compsust/openCollector/Website_Development/images/nathaniel.jpg

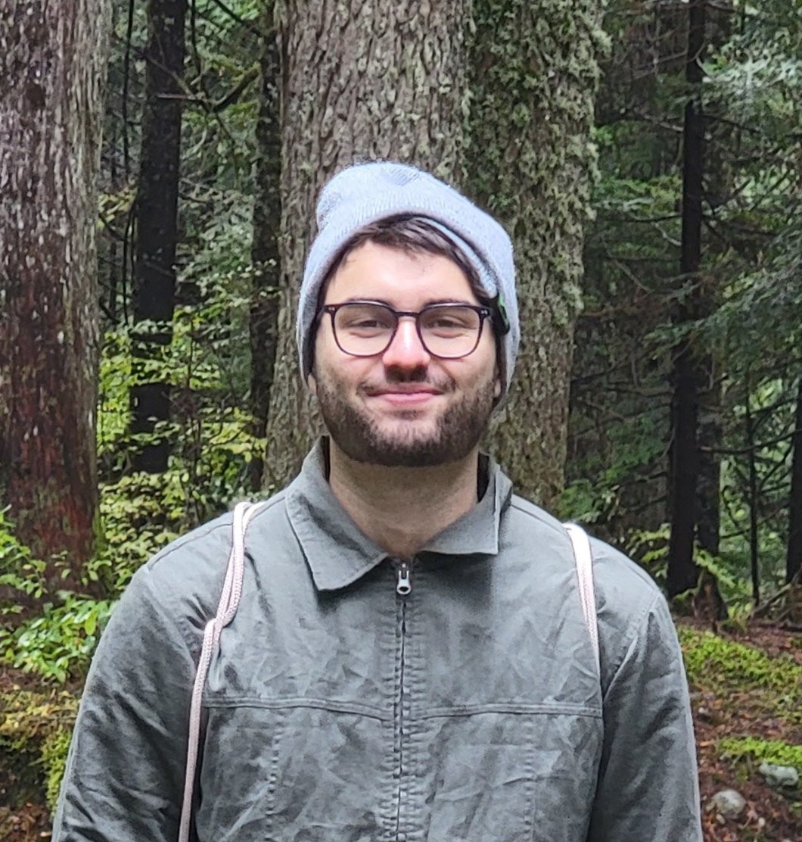
Website_Development/images/nathaniel.jpg
