compsust/openCollector/Website_Development/images/tianna.jpg

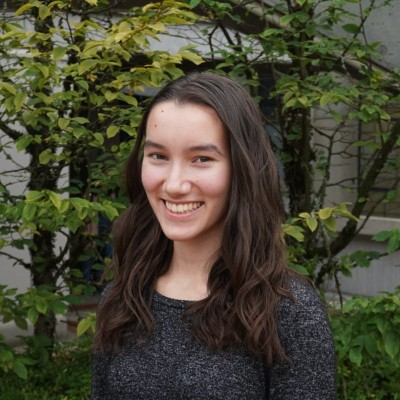
Website_Development/images/tianna.jpg
