compsust/openCollector/collector/src/sensors/drivers/DHT20/micropython.py

# MC: 02/21/2025, Complete implmentation
# MC: 03/07/2025, Added initilization

import machine
import utime

from ....config import SensorConfig
from ....datastructures import SensorData
from ...driver import AbstractSensorDriver


class DHT20SensorDriverMicropython(AbstractSensorDriver):
    """
    Implementation of the Dht20 Sensor Driver for micropython.
    """

    def __init__(self, config: SensorConfig):
        """Initialize the sensor driver with an I2C instance."""
        self.i2c = machine.I2C(
            0, scl=machine.Pin(config.gpio["SCL"]), sda=machine.Pin(config.gpio["SDA"])
        )
        self.address = 0x38  # Default I2C address for DHT20

    def poll(self) -> SensorData:
        """
        collects sensor data from DHT20
        Args:
            i2c object. Ex: i2c = machine.I2C(0, scl=machine.Pin(27), sda=machine.Pin(26))
        Returns:
            SensorData: The temperature and humidity data returned by the sensor.
        """

        status = self.i2c.readfrom(0x38, 1)
        if status[0] != 0x18:
            raise Exception("DHT20 Error: Checksum Fail")

        # ask for measurement
        utime.sleep_ms(50)
        self.i2c.writeto(0x38, bytes([0xAC, 0x33, 0x00]))
        utime.sleep_ms(80)

        # check if measurment is complete
        counter = 0
        while True:
            status = self.i2c.readfrom(0x38, 1)
            status_bit7 = (status[0] & 0x80) == 0  # Extract Bit [7]
            if status_bit7:  # If Bit [7] == 0, measurement is complete
                break
            elif counter > 10:
                raise Exception("DHT20 Error: Measurement Timeout")
            else:
                utime.sleep_ms(80)  # Wait 80ms before checking again
                counter += 1

        # data processing
        data = self.i2c.readfrom(0x38, 7)  # Read 6 bytes of data
        hum = (data[1] << 12 | data[2] << 4 | data[3] >> 4) / (2**20) * 100
        temp = ((data[3] << 16 | data[4] << 8 | data[5]) & 0xFFFFF) / (2**20) * 200 - 50
        return {"temperature": temp, "humidity": hum}
